andres-garcia-alves/electronics-memory-game/Resources/09-project-final-01.jpg

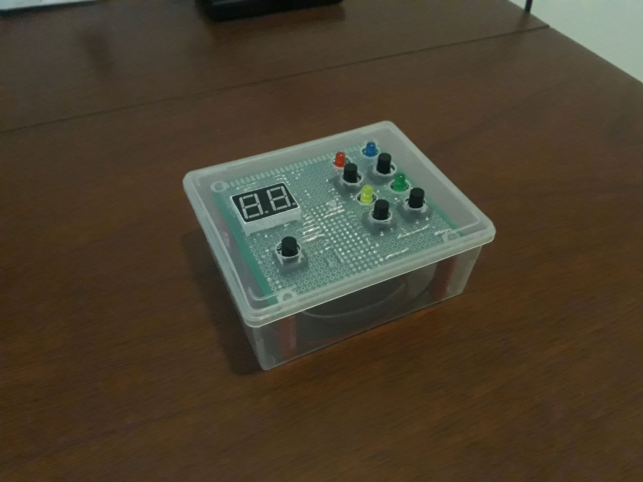
Resources/09-project-final-01.jpg
